DienKiku/Indoor-Air-Quality-Project/src/firmware/firebase_config.h

#ifndef FIREBASE_CONFIG_H
#define FIREBASE_CONFIG_H

// ==========================================
// WI-FI CREDENTIALS
// ==========================================
#define WIFI_SSID           "Aeduongso8"
#define WIFI_PASSWORD       "20022003"

// ==========================================
// GOOGLE FIREBASE CREDENTIALS
// ==========================================
#define FIREBASE_HOST       "https://iaq-project-57a4f-default-rtdb.asia-southeast1.firebasedatabase.app/"
#define FIREBASE_AUTH       "CIX0VQNsdwG4iaeeTnJqAW9VH1q79wumwuPuUZ49"

// Device Identifier in Firebase Realtime Database
#define DEVICE_ID           "ESP32C3_STATION_01"

#endif // FIREBASE_CONFIG_H
